matiasmicheletto/water-flow-meter/schematics/water-flow-meter-schematics.kicad_pcb

## KiCad design docs/schema/JBE_CRT_Controller/JBE_CRT_Controller.kicad_sch

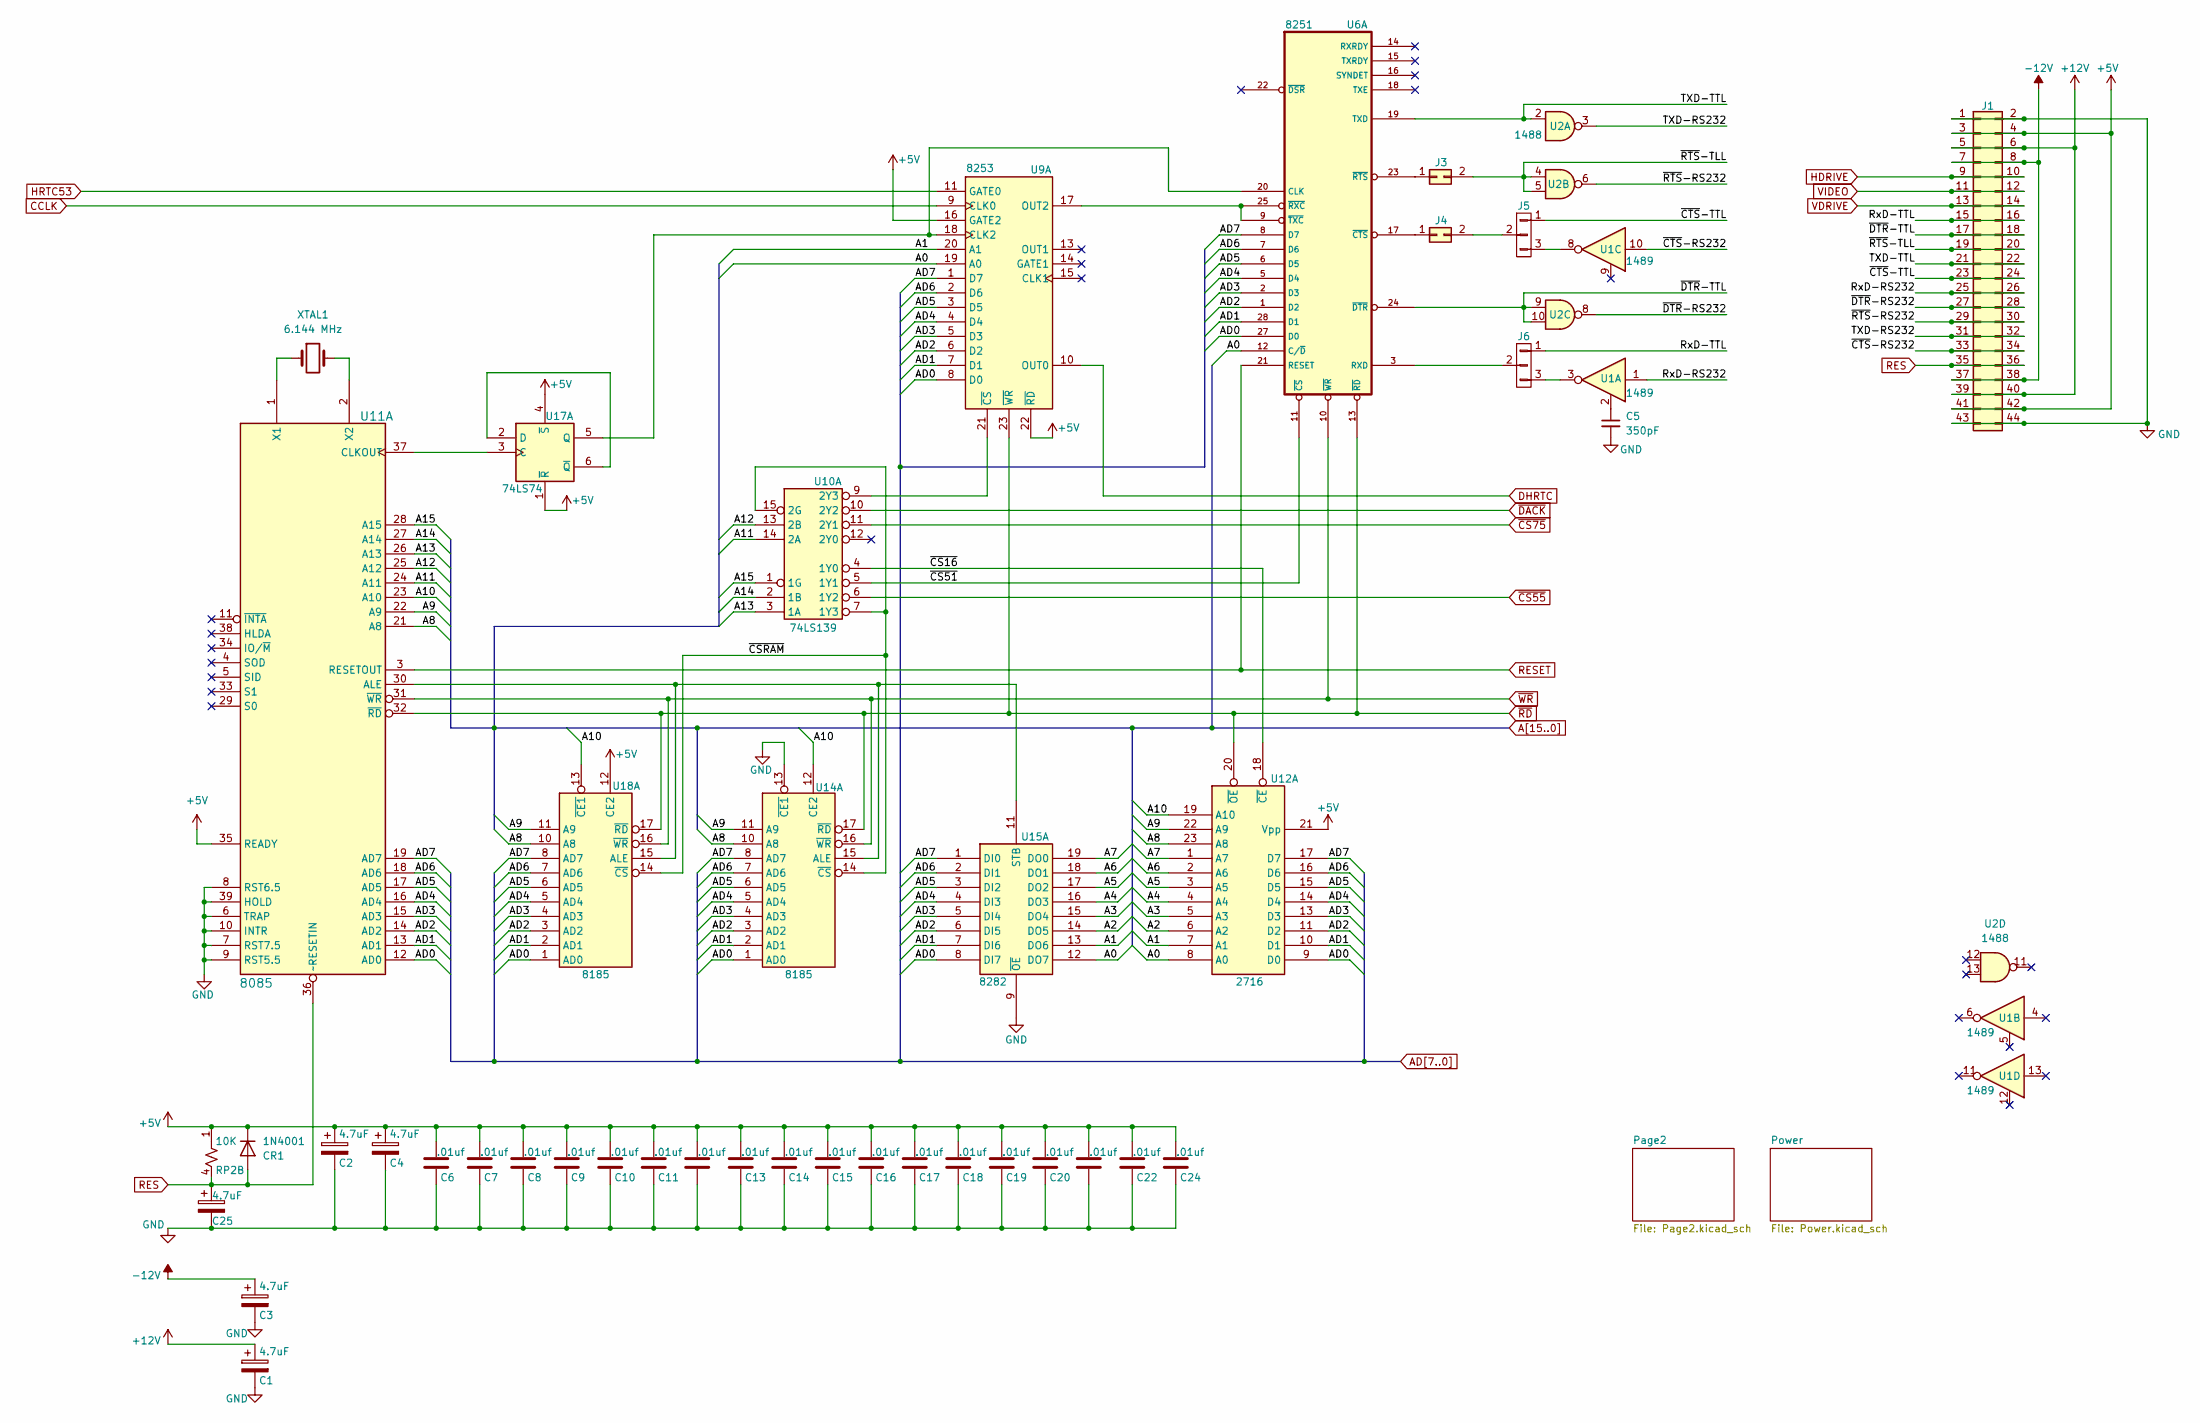
[picture p5: schematic JBE_CRT_Controller.kicad_sch]

Parts:
C1, C2, C3, C4, C25: 4.7uF
C5: 350pF
C6, C7, C8, C9, C10, C11, C12, C13, C14, C15, C16, C17, C18, C19, C20, C21, C22, C24: .01uf
CR1: 1N4001
J1: Conn_02x22_Odd_Even
J3, J4: Conn_01x02
J5, J6: Conn_01x03
RP2: 10K
U1: 1489
U2: 1488
U6: 8251
U9: 8253; DIP-24_W15.24mm
U10: 74LS139
U11: 8085; DIP-40_W25.4mm
U12: 2716
U14, U18: 8185
U15: 8282
U17: 74LS74
XTAL1: 6.144 MHz

Connections:
+5V: C2.1, C4.1, C6.1, C7.1, C8.1, C9.1, C10.1, C11.1, C12.1, C13.1, C14.1, C15.1, C16.1, C17.1, C18.1, C19.1, C20.1, C21.1, C22.1, C24.1, CR1.1 (K), J1.3, J1.4, J1.41, J1.42, RP2.1, U9.16 (GATE2), U9.22 (~RD), U11.35 (READY), U12.21 (Vpp), U17.1 (~R), U17.4 (~S), U18.12 (CE2)
+12V: C1.1, J1.5, J1.6, J1.39, J1.40
-12V: C3.1, J1.7, J1.8, J1.37, J1.38
A0: U6.12 (C/~D), U9.19 (A0), U12.8 (A0), U15.12 (DO7)
A1: U9.20 (A1), U12.7 (A1), U15.13 (DO6)
A2: U12.6 (A2), U15.14 (DO5)
A3: U12.5 (A3), U15.15 (DO4)
A4: U12.4 (A4), U15.16 (DO3)
A5: U12.3 (A5), U15.17 (DO2)
A6: U12.2 (A6), U15.18 (DO1)
A7: U12.1 (A7), U15.19 (DO0)
A8: U11.21 (A8), U12.23 (A8), U14.10 (A8), U18.10 (A8)
A9: U11.22 (A9), U12.22 (A9), U14.11 (A9), U18.11 (A9)
A10: U11.23 (A10), U12.19 (A10), U14.12 (CE2), U18.13 (~CE1)
A11: U10.14 (2A), U11.24 (A11)
A12: U10.13 (2B), U11.25 (A12)
A13: U10.3 (1A), U11.26 (A13)
A14: U10.2 (1B), U11.27 (A14)
A15: U10.1 (1G), U11.28 (A15)
AD0: U6.27 (D0), U9.8 (D0), U11.12 (AD0), U12.9 (D0), U14.1 (AD0), U15.8 (DI7), U18.1 (AD0)
AD1: U6.28 (D1), U9.7 (D1), U11.13 (AD1), U12.10 (D1), U14.2 (AD1), U15.7 (DI6), U18.2 (AD1)
AD2: U6.1 (D2), U9.6 (D2), U11.14 (AD2), U12.11 (D2), U14.3 (AD2), U15.6 (DI5), U18.3 (AD2)
AD3: U6.2 (D3), U9.5 (D3), U11.15 (AD3), U12.13 (D3), U14.4 (AD3), U15.5 (DI4), U18.4 (AD3)
AD4: U6.5 (D4), U9.4 (D4), U11.16 (AD4), U12.14 (D4), U14.5 (AD4), U15.4 (DI3), U18.5 (AD4)
AD5: U6.6 (D5), U9.3 (D5), U11.17 (AD5), U12.15 (D5), U14.6 (AD5), U15.3 (DI2), U18.6 (AD5)
AD6: U6.7 (D6), U9.2 (D6), U11.18 (AD6), U12.16 (D6), U14.7 (AD6), U15.2 (DI1), U18.7 (AD6)
AD7: U6.8 (D7), U9.1 (D7), U11.19 (AD7), U12.17 (D7), U14.8 (AD7), U15.1 (DI0), U18.8 (AD7)
CCLK: U9.9 (CLK0)
DHRTC: U9.10 (OUT0)
GND: C1.2, C2.2, C3.2, C4.2, C5.2, C6.2, C7.2, C8.2, C9.2, C10.2, C11.2, C12.2, C13.2, C14.2, C15.2, C16.2, C17.2, C18.2, C19.2, C20.2, C21.2, C22.2, C24.2, C25.2, J1.1, J1.2, J1.43, J1.44, U11.6 (TRAP), U11.7 (RST7.5), U11.8 (RST6.5), U11.9 (RST5.5), U11.10 (INTR), U11.39 (HOLD), U14.13 (~CE1), U15.9 (~OE)
HDRIVE: J1.9, J1.10
HRTC53: U9.11 (GATE0)
unnamed: C5.1, U1.2
unnamed: J3.1, U6.23 (~RTS)
unnamed: J4.1, U6.17 (~CTS)
unnamed: J4.2, J5.2
unnamed: J5.3, U1.8
unnamed: J6.2, U6.3 (RXD)
unnamed: J6.3, U1.3
unnamed: U6.9 (~TXC), U6.25 (~RXC), U9.17 (OUT2)
unnamed: U9.21 (~CS), U10.9 (2Y3)
unnamed: U11.1 (X1), XTAL1.1
unnamed: U11.2 (X2), XTAL1.2
unnamed: U11.30 (ALE), U14.15 (ALE), U15.11 (STB), U18.15 (ALE)
unnamed: U11.37 (CLKOUT), U17.3 (C)
unnamed: U17.2 (D), U17.6 (~Q)
unnamed: U6.20 (CLK), U9.18 (CLK2), U17.5 (Q)
RES: C25.1, CR1.2 (A), J1.35, J1.36, RP2.4, U11.36 (~RESETIN)
RESET: U6.21 (RESET), U11.3 (RESETOUT)
RxD-RS232: J1.25, J1.26, U1.1
RxD-TTL: J1.15, J1.16, J6.1
TXD-RS232: J1.31, J1.32, U2.3
TXD-TTL: J1.21, J1.22, U2.2, U6.19 (TXD)
VDRIVE: J1.13, J1.14
VIDEO: J1.11, J1.12
~CS16: U10.4 (1Y0), U12.18 (~CE)
~CS51: U6.11 (~CS), U10.5 (1Y1)
~CS55: U10.6 (1Y2)
~CS75: U10.11 (2Y1)
~CSRAM: U10.7 (1Y3), U10.15 (2G), U14.14 (~CS), U18.14 (~CS)
~CTS-RS232: J1.33, J1.34, U1.10
~CTS-TTL: J1.23, J1.24, J5.1
~DACK: U10.10 (2Y2)
~DTR-RS232: J1.27, J1.28, U2.8
~DTR-TTL: J1.17, J1.18, U2.9, U2.10, U6.24 (~DTR)
~RD: U6.13 (~RD), U9.23 (~WR), U11.32 (~RD), U12.20 (~OE), U14.17 (~RD), U18.17 (~RD)
~RTS-RS232: J1.29, J1.30, U2.6
~RTS-TLL: J1.19, J1.20, J3.2, U2.4, U2.5
~WR: U6.10 (~WR), U11.31 (~WR), U14.16 (~WR), U18.16 (~WR)
