matiasmicheletto/water-flow-meter/schematics/water-flow-meter-schematics.kicad_pcb

## KiCad design docs/schema/JBE_CRT_Controller/Power.kicad_sch

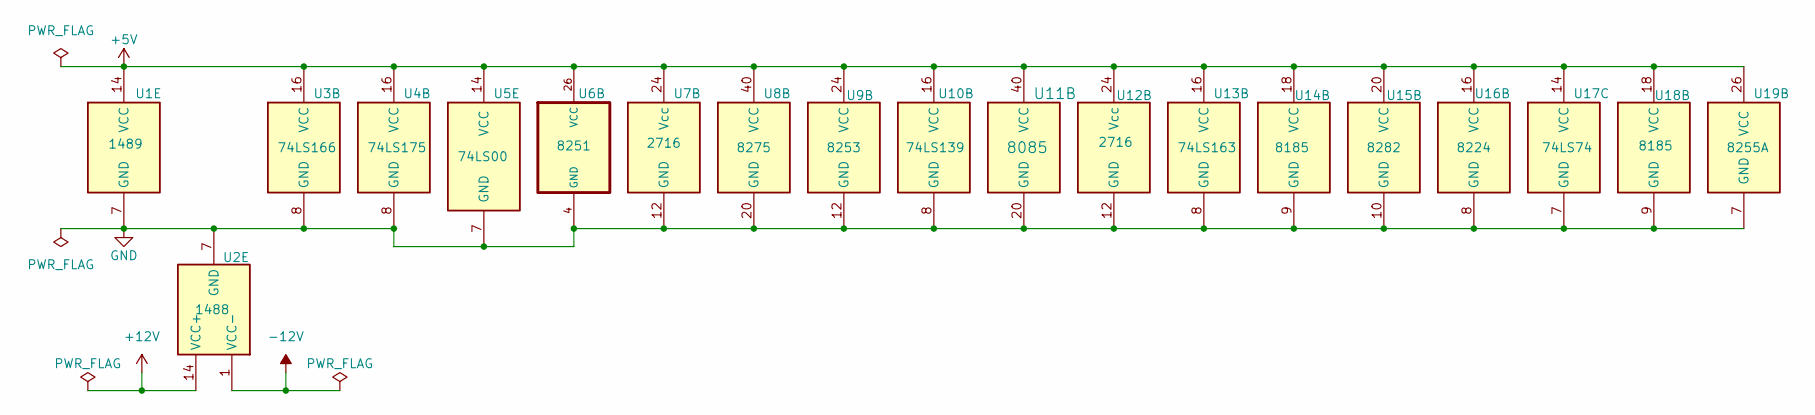
[picture p7: schematic Power.kicad_sch]

Parts:
U1: 1489
U2: 1488
U3: 74LS166
U4: 74LS175
U5: 74LS00
U6: 8251
U7, U12: 2716
U8: 8275
U9: 8253; DIP-24_W15.24mm
U10: 74LS139
U11: 8085; DIP-40_W25.4mm
U13: 74LS163
U14, U18: 8185
U15: 8282
U16: 8224; DIP-16_W7.62mm
U17: 74LS74
U19: 8255A; DIP-40_W15.24mm

Connections:
+5V: U1.14 (VCC), U3.16 (VCC), U4.16 (VCC), U5.14 (VCC), U6.26 (VCC), U7.24 (Vcc), U8.40 (VCC), U9.24 (VCC), U10.16 (VCC), U11.40 (VCC), U12.24 (Vcc), U13.16 (VCC), U14.18 (VCC), U15.20 (VCC), U16.16 (VCC), U17.14 (VCC), U18.18 (VCC), U19.26 (VCC)
+12V: U2.14 (VCC+)
-12V: U2.1 (VCC-)
GND: U1.7 (GND), U2.7 (GND), U3.8 (GND), U4.8 (GND), U5.7 (GND), U6.4 (GND), U7.12 (GND), U8.20 (GND), U9.12 (GND), U10.8 (GND), U11.20 (GND), U12.12 (GND), U13.8 (GND), U14.9 (GND), U15.10 (GND), U16.8 (GND), U17.7 (GND), U18.9 (GND), U19.7 (GND)
